valtttu/DIY-suspension-wizard/Documentation/Figures/brake_sensor_3.jpg

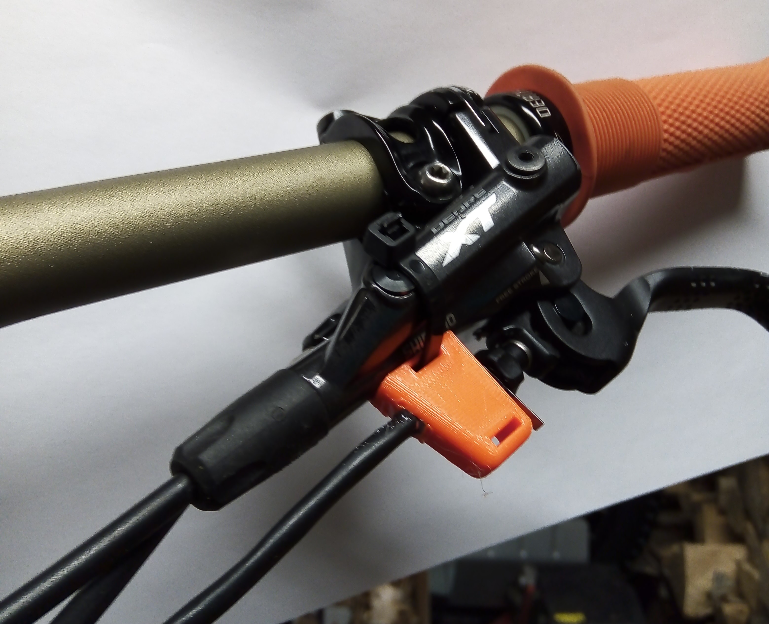
Documentation/Figures/brake_sensor_3.jpg
