valtttu/DIY-suspension-wizard/Documentation/Figures/enc_3.jpg

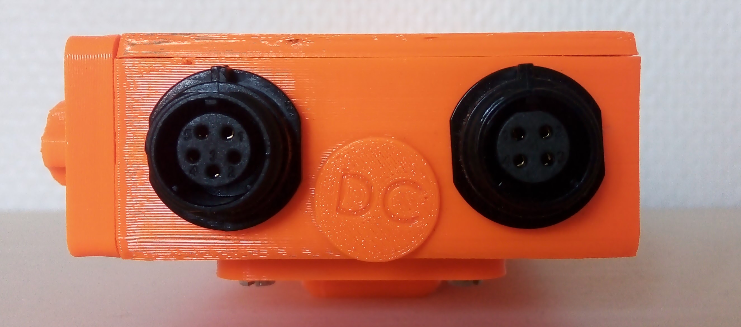
Documentation/Figures/enc_3.jpg
