valtttu/DIY-suspension-wizard/Documentation/Figures/enc_4.jpg

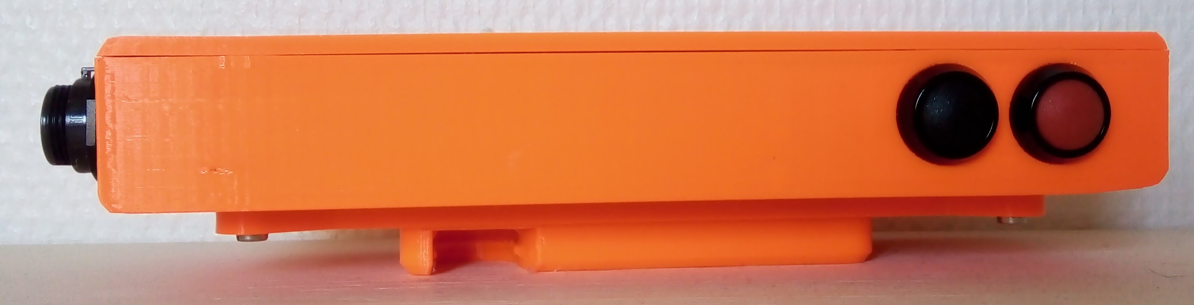
Documentation/Figures/enc_4.jpg
