valtttu/DIY-suspension-wizard/Documentation/Figures/enc_5.jpg

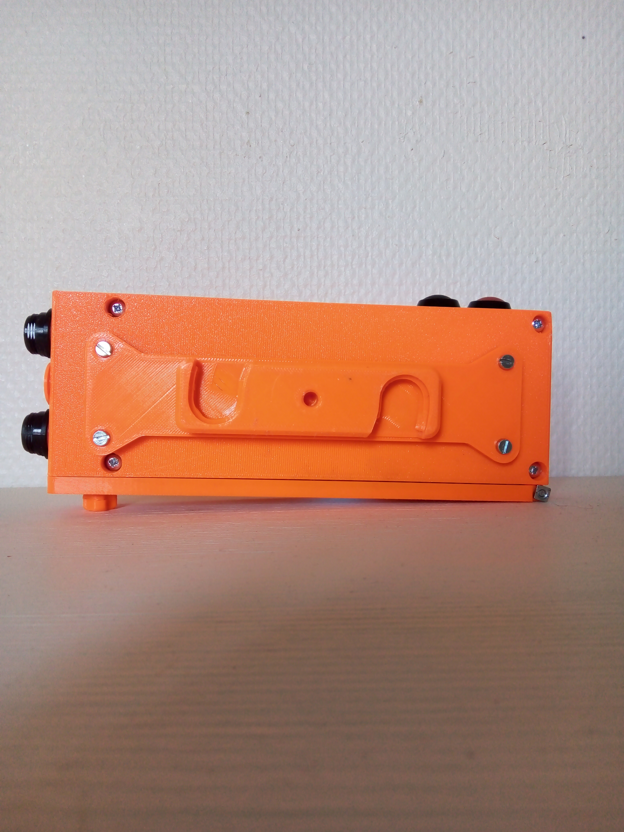
Documentation/Figures/enc_5.jpg
