valtttu/DIY-suspension-wizard/Documentation/Figures/enc_6.jpg

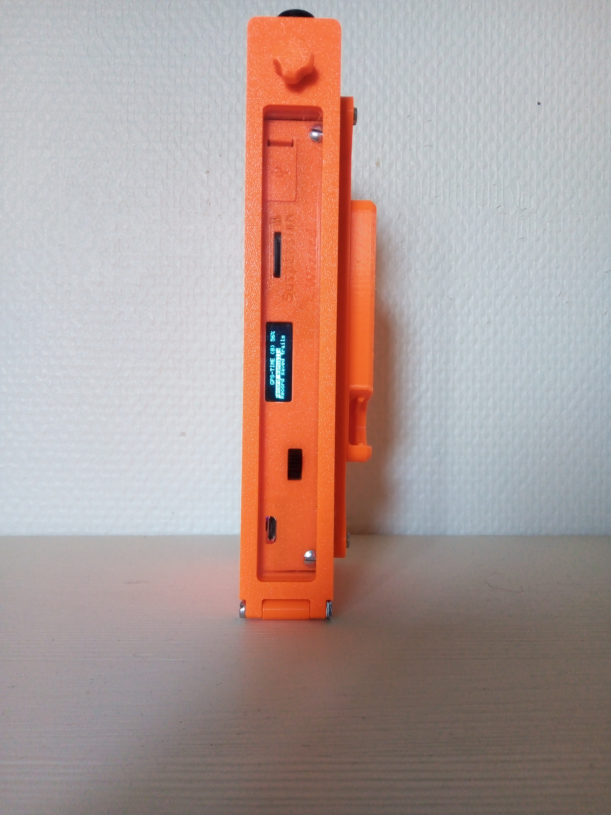
Documentation/Figures/enc_6.jpg
