valtttu/DIY-suspension-wizard/Documentation/Figures/enc_9.jpg

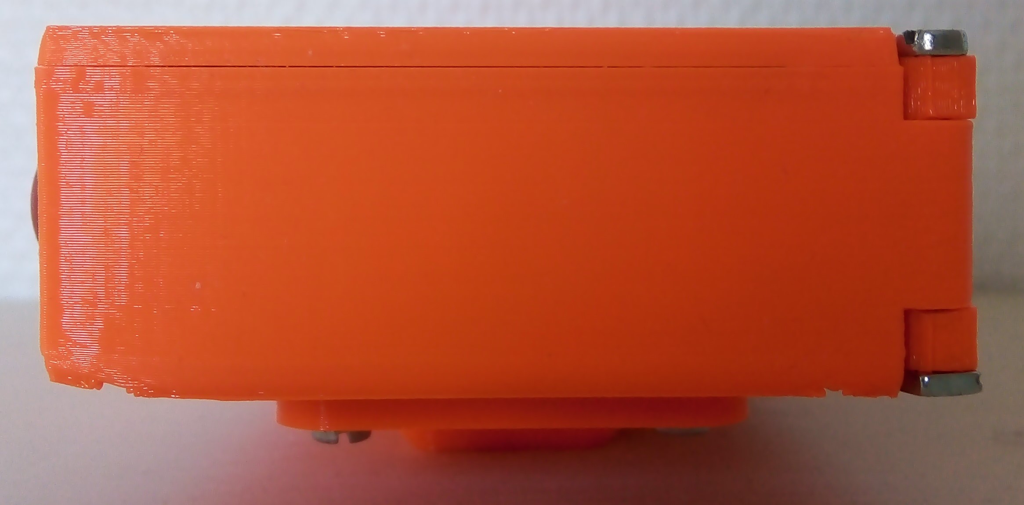
Documentation/Figures/enc_9.jpg
