valtttu/DIY-suspension-wizard/Documentation/Figures/pcb_front.jpg

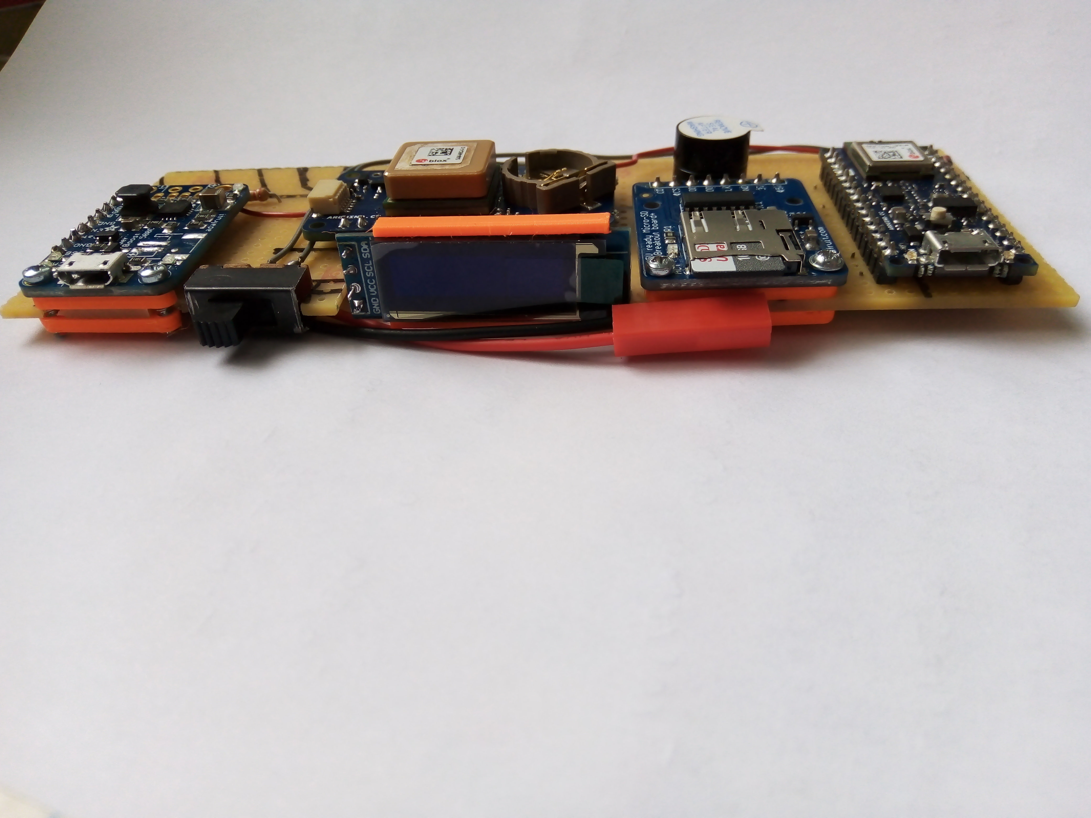
Documentation/Figures/pcb_front.jpg
