valtttu/DIY-suspension-wizard/Documentation/Figures/sensor_v1.jpg

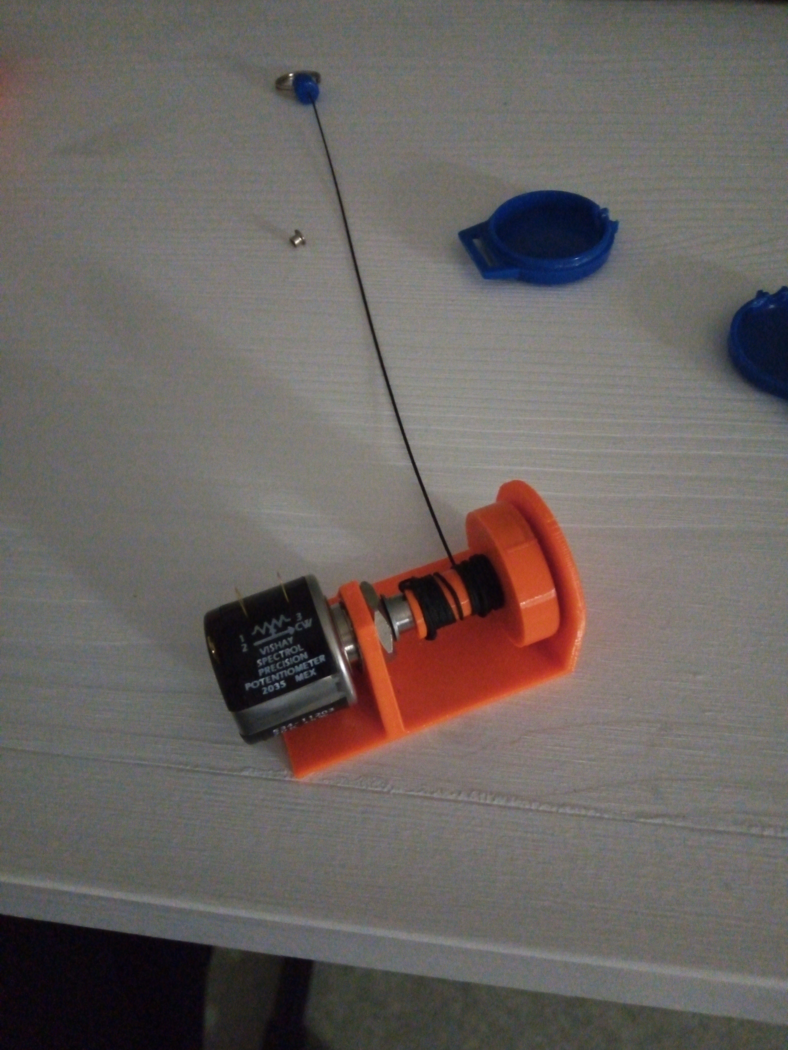
Documentation/Figures/sensor_v1.jpg
