valtttu/DIY-suspension-wizard/Documentation/Figures/sensor_v2_1.jpg

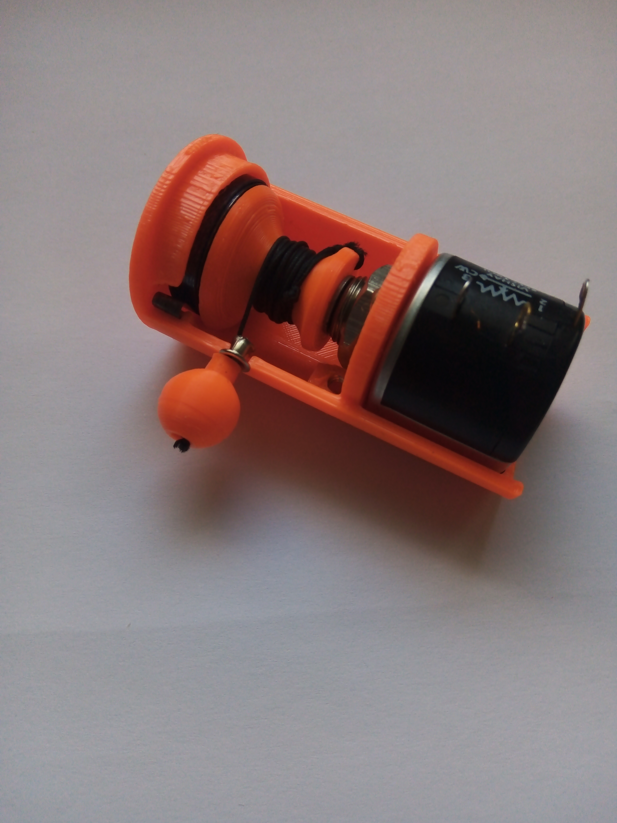
Documentation/Figures/sensor_v2_1.jpg
