valtttu/DIY-suspension-wizard/3D models/enclosure_front_plate.STL

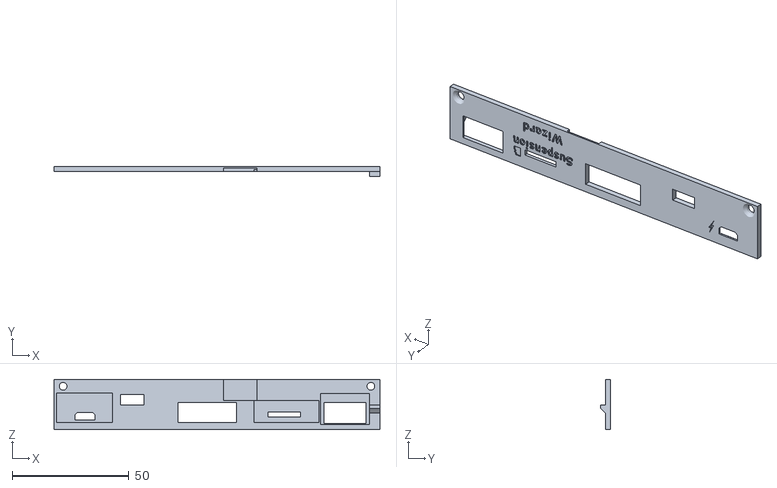
[picture p45: CAD file, 2023-01-10]
3D models/enclosure_front_plate.STL
139.5 x 4.10 x 21.6
