valtttu/DIY-suspension-wizard/3D models/pcb_254_spacer.STL

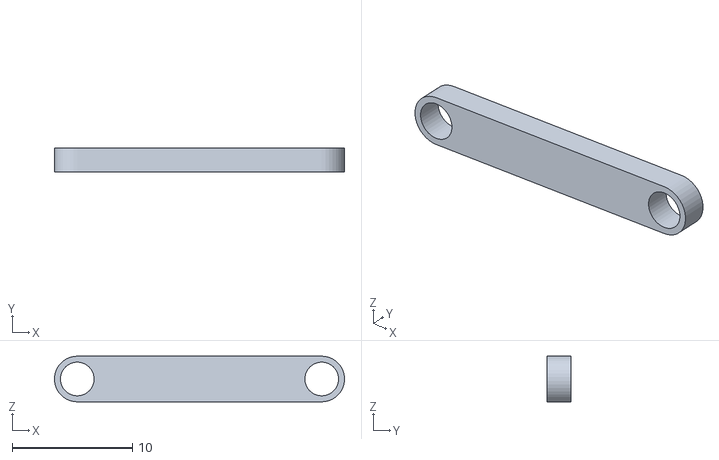
[picture p46: CAD file, 2023-01-10]
3D models/pcb_254_spacer.STL
24.1 x 2.00 x 3.80
