valtttu/DIY-suspension-wizard/3D models/enclosure_battery_holder.STL

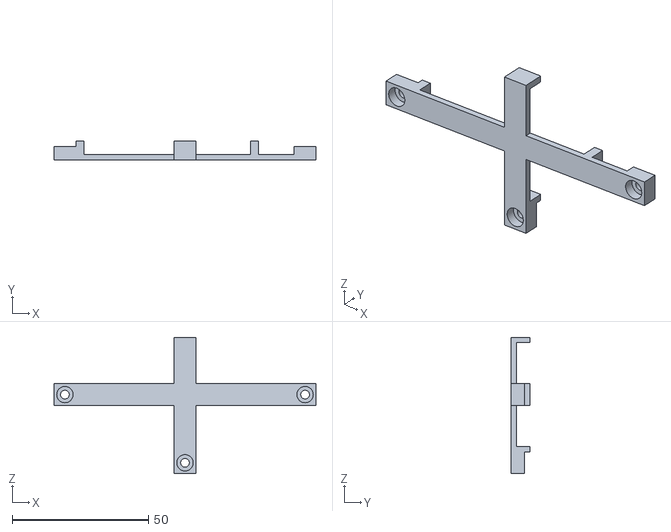
[picture p47: CAD file, 2023-01-10]
3D models/enclosure_battery_holder.STL
96.0 x 7.00 x 50.0
