valtttu/DIY-suspension-wizard/3D models/pcb_1944_spacer.STL

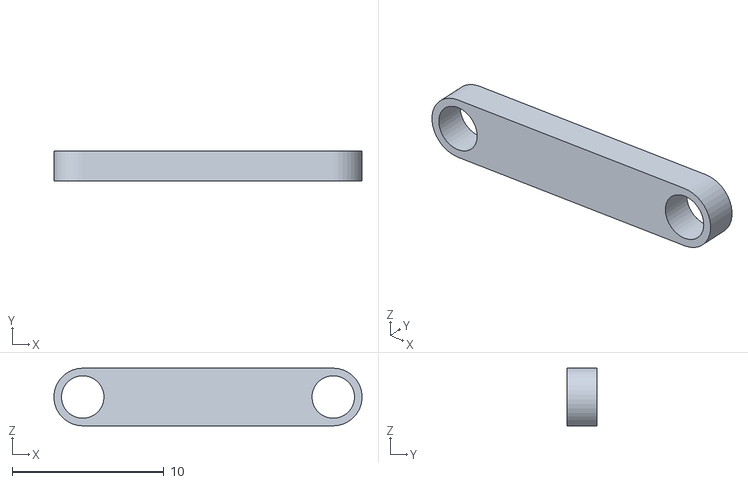
[picture p48: CAD file, 2023-01-10]
3D models/pcb_1944_spacer.STL
20.3 x 2.00 x 3.80
