valtttu/DIY-suspension-wizard/3D models/brake_sensor.STL

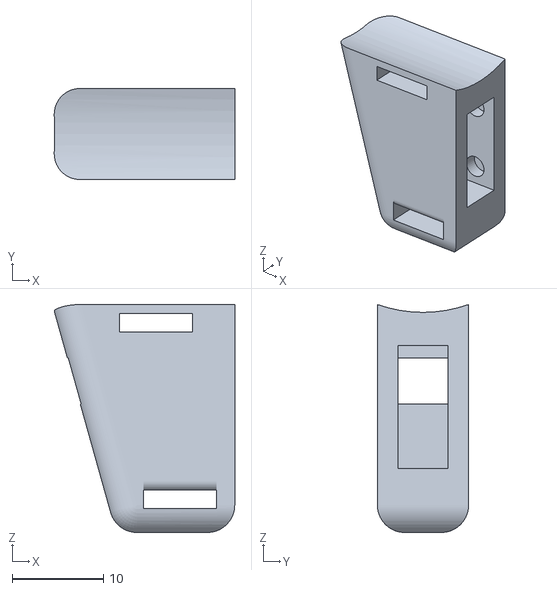
[picture p49: CAD file, 2023-01-10]
3D models/brake_sensor.STL
19.8 x 10.00 x 25.0
