valtttu/DIY-suspension-wizard/3D models/pot_adapter_m5.STL

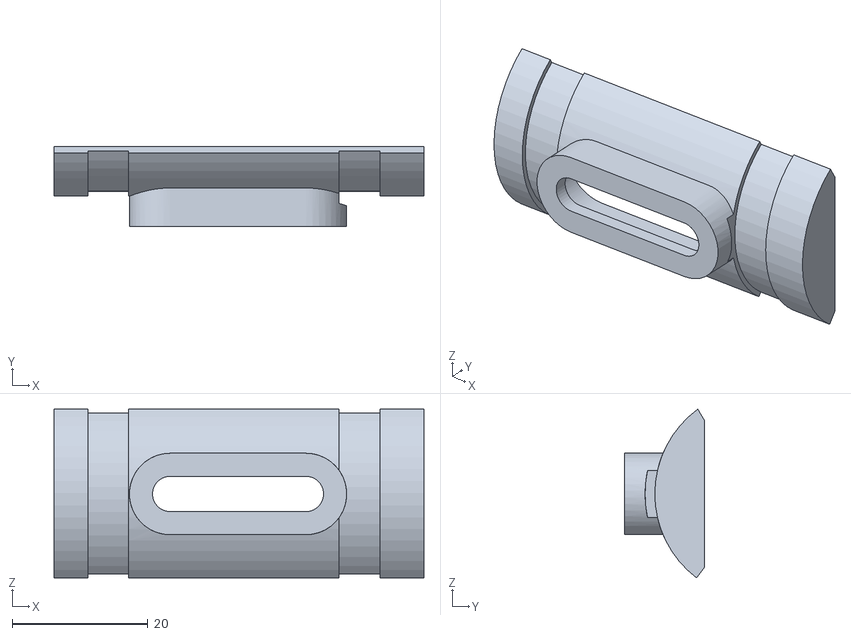
[picture p50: CAD file, 2023-01-10]
3D models/pot_adapter_m5.STL
54.5 x 11.9 x 24.9
