valtttu/DIY-suspension-wizard/3D models/enclosure_lid.STL

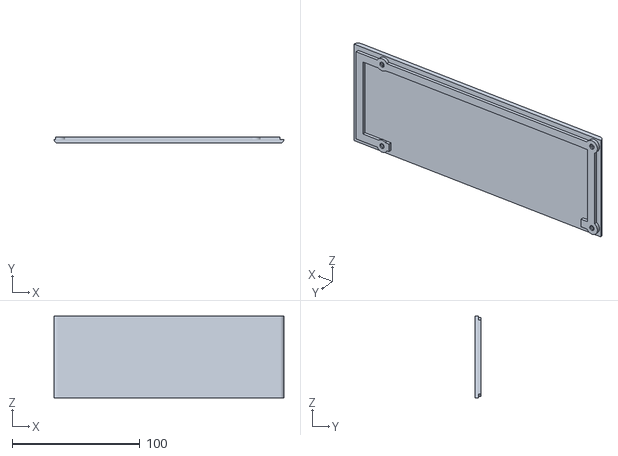
[picture p51: CAD file, 2023-01-10]
3D models/enclosure_lid.STL
180.0 x 5.00 x 64.0
