valtttu/DIY-suspension-wizard/3D models/pot_ball_joint.STL

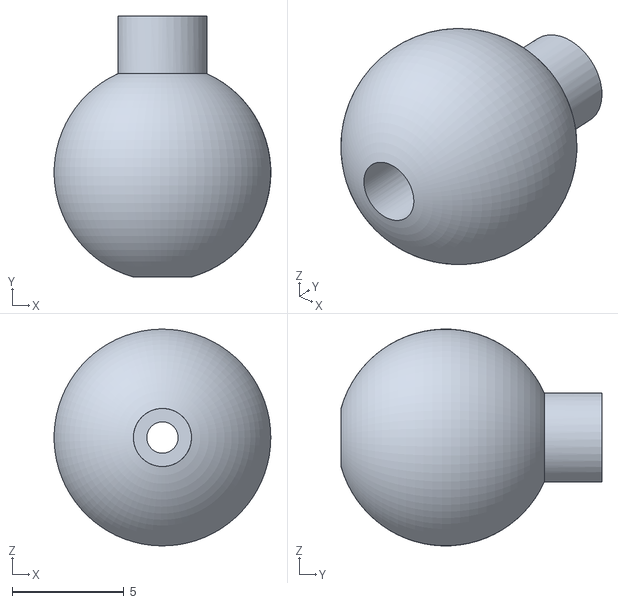
[picture p52: CAD file, 2023-01-10]
3D models/pot_ball_joint.STL
9.69 x 11.7 x 9.69
