valtttu/DIY-suspension-wizard/3D models/pot_cover_top.STL

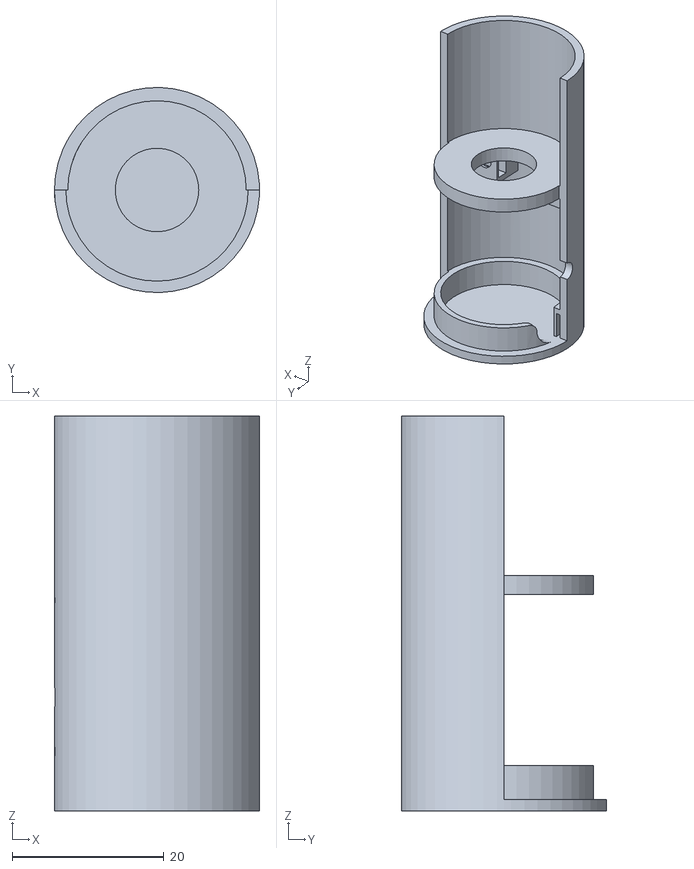
[picture p53: CAD file, 2023-01-10]
3D models/pot_cover_top.STL
27.0 x 27.0 x 52.0
