valtttu/DIY-suspension-wizard/3D models/pot_reel.STL

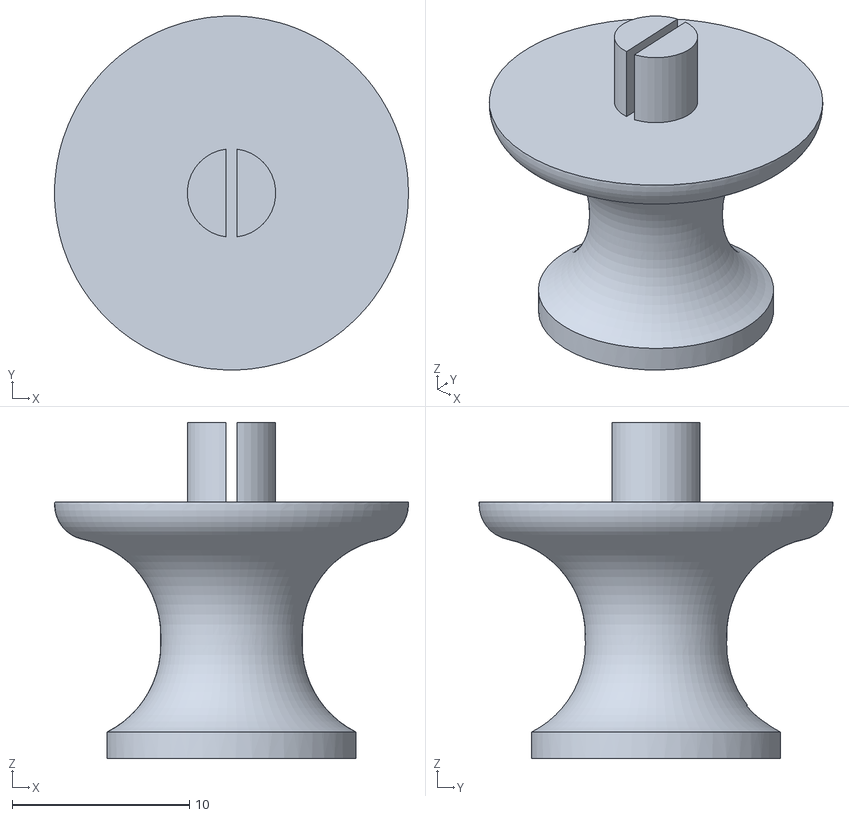
[picture p54: CAD file, 2023-01-10]
3D models/pot_reel.STL
20.0 x 20.0 x 19.0
