valtttu/DIY-suspension-wizard/3D models/enclosure_door.STL

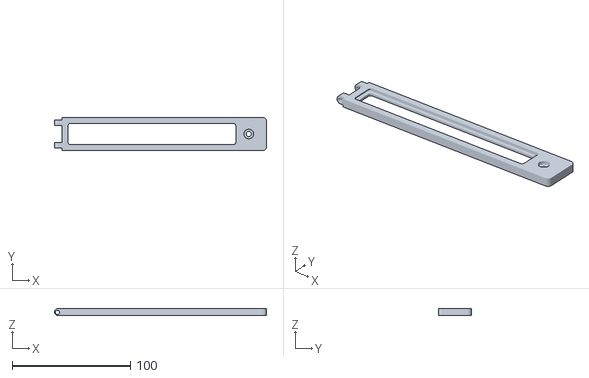
[picture p55: CAD file, 2023-01-10]
3D models/enclosure_door.STL
179.5 x 28.0 x 6.00
