valtttu/DIY-suspension-wizard/3D models/enclosure_sensor_cap.STL

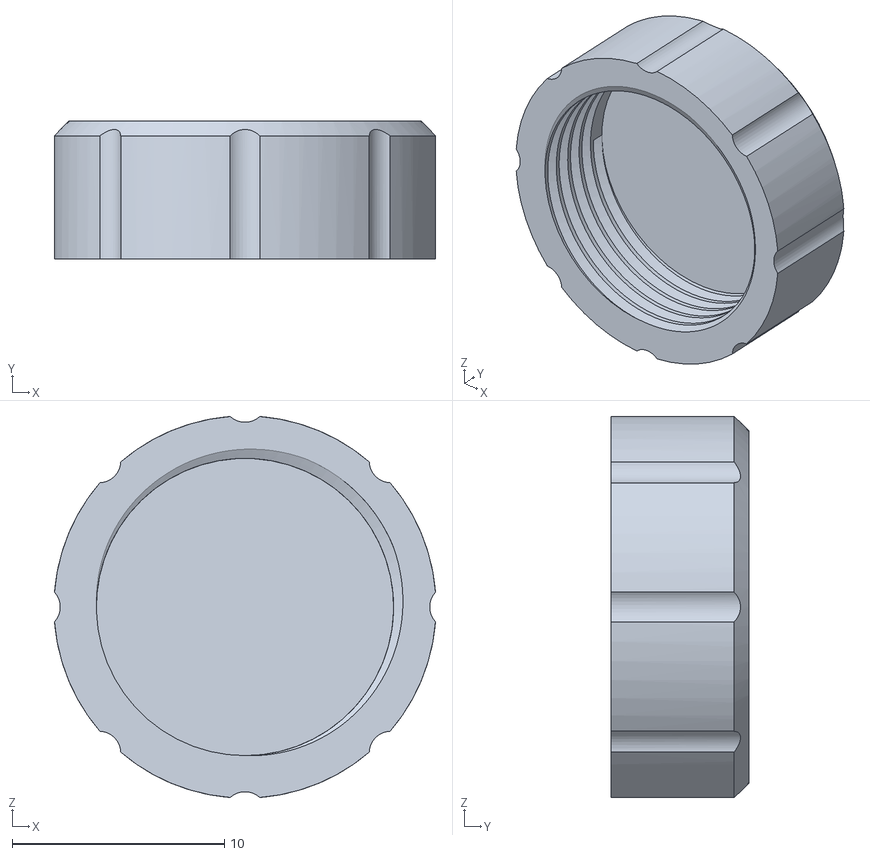
[picture p56: CAD file, 2023-01-10]
3D models/enclosure_sensor_cap.STL
17.9 x 6.50 x 17.9
